4920616d20546f6d/Nintendo_Famicom_Console/CONTROLLER1/pcb_front.jpg

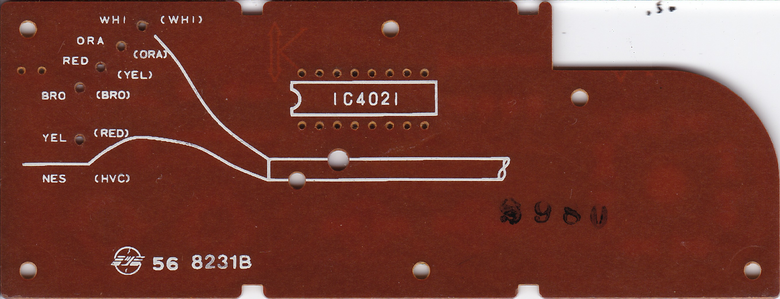
CONTROLLER1/pcb_front.jpg
