4920616d20546f6d/Nintendo_Famicom_Console/CONTROLLER2/pcb_front_fullscan.jpg

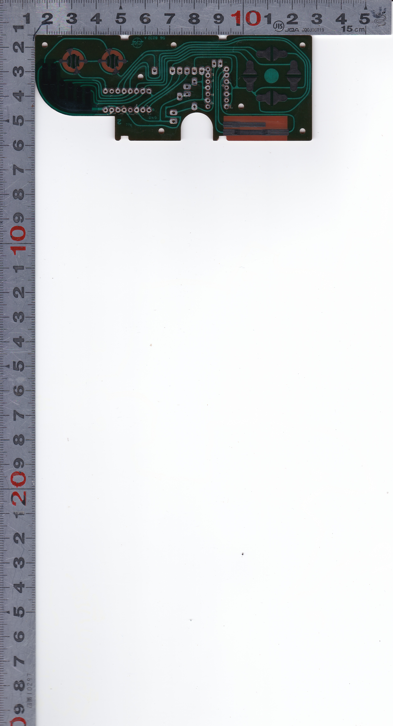
CONTROLLER2/pcb_front_fullscan.jpg
