4920616d20546f6d/Nintendo_Famicom_Console/HVC-CPU-GPM-02/pcb_rear_render.png

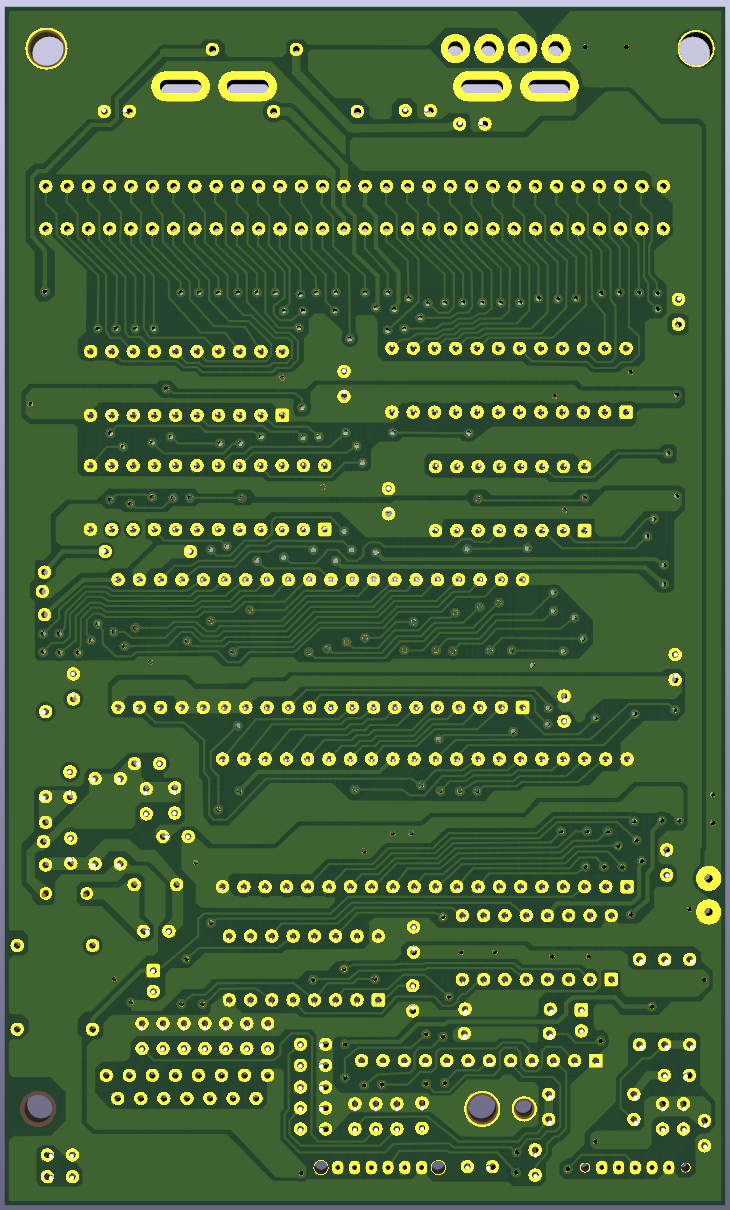
HVC-CPU-GPM-02/pcb_rear_render.png
