4920616d20546f6d/Nintendo_Famicom_Console/images/FC console RF+Power module front.jpg

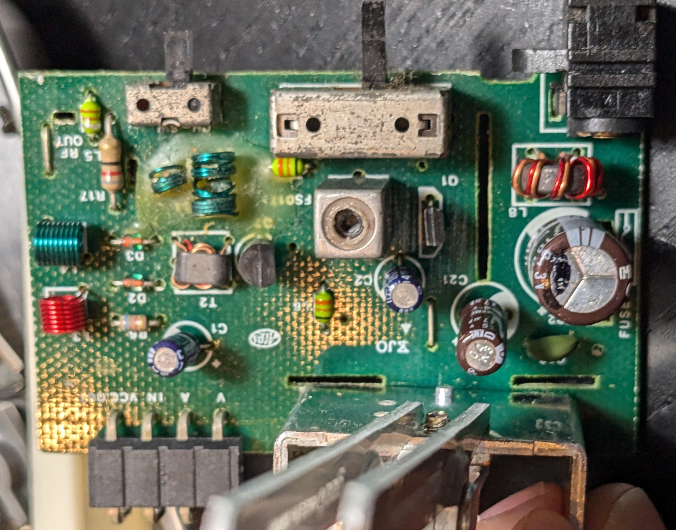
images/FC console RF+Power module front.jpg
