4920616d20546f6d/Nintendo_Famicom_Console/patents/RP2A03_-_PSG_-_Patent_Diagram_-_9.png

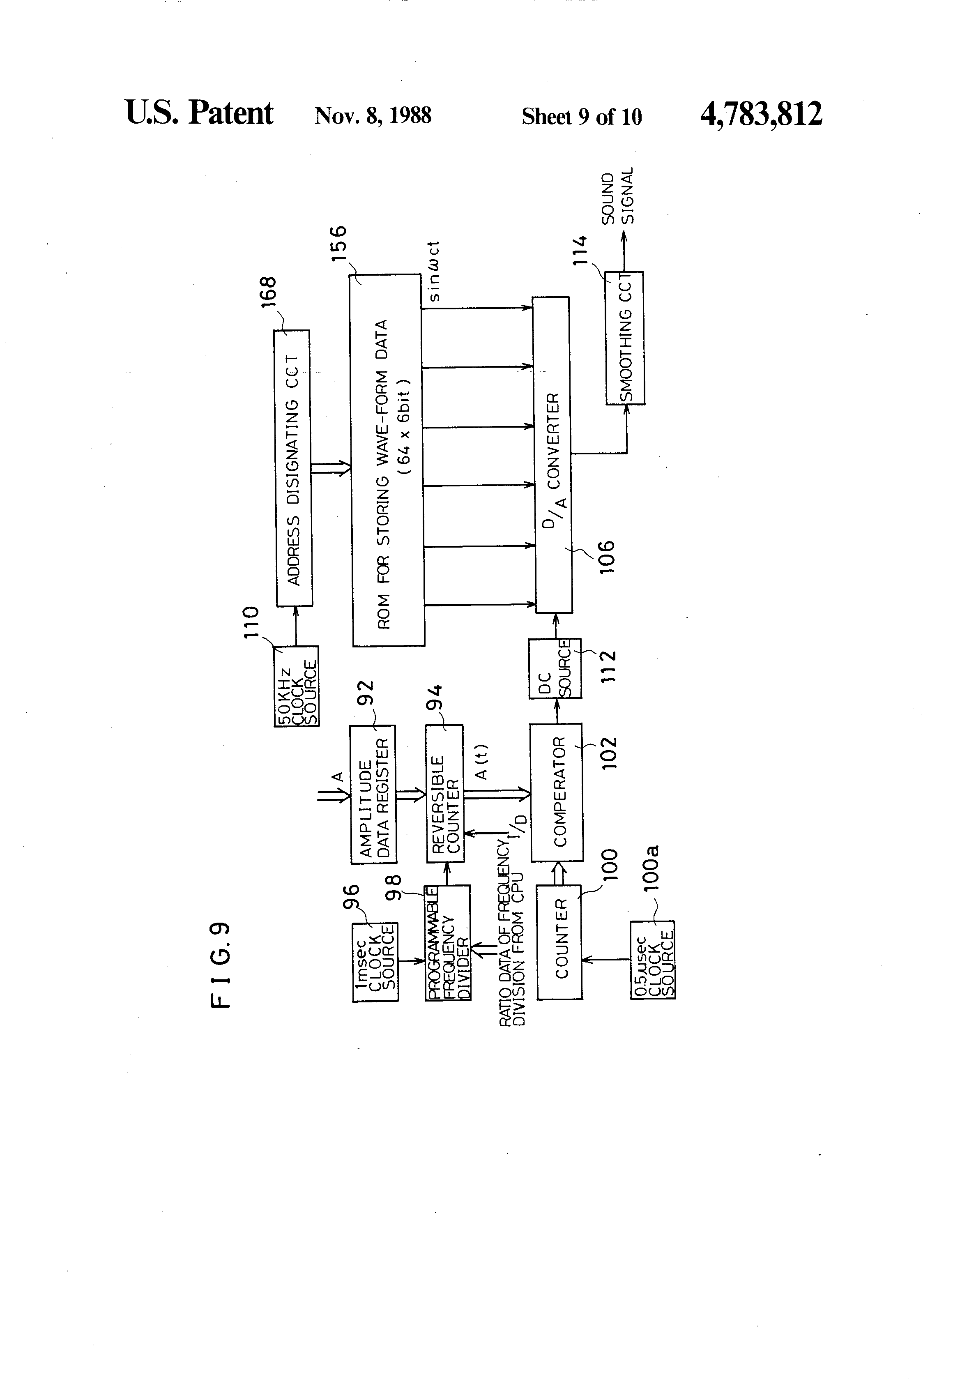
patents/RP2A03_-_PSG_-_Patent_Diagram_-_9.png
