4920616d20546f6d/Nintendo_Famicom_Console/RF_MODULE/pcb_front.jpg

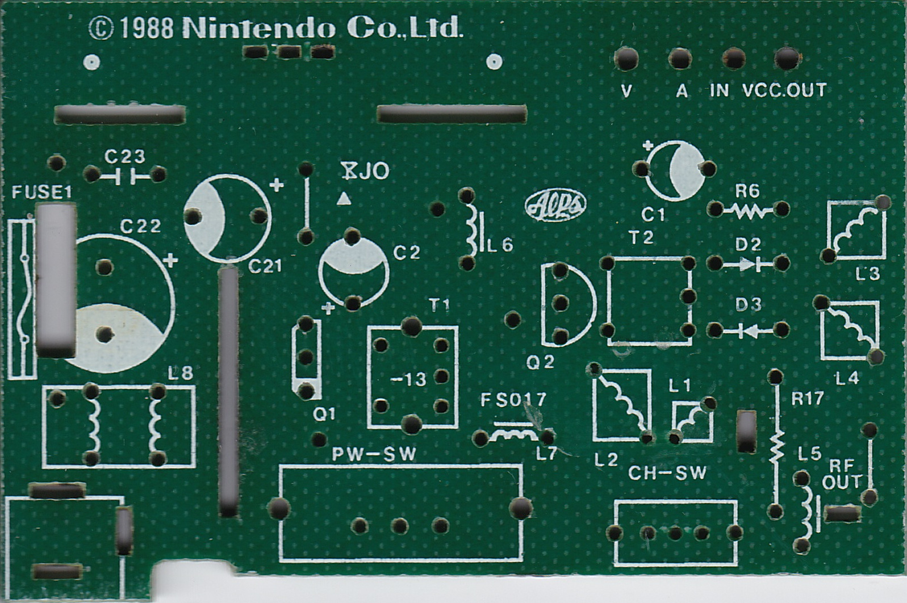
RF_MODULE/pcb_front.jpg
