4920616d20546f6d/Nintendo_Famicom_Console/RF_SWITCH/pcb_back_fullscan.jpg

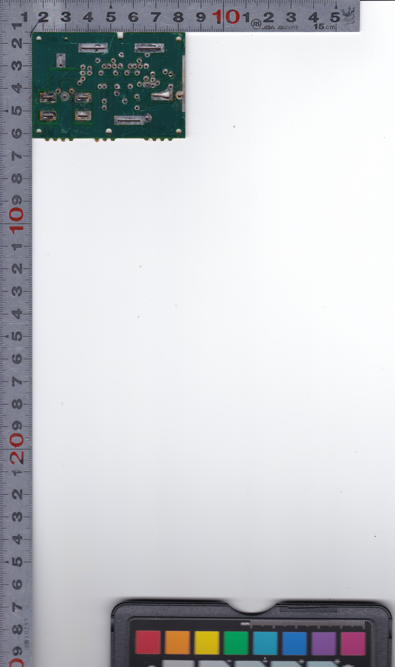
RF_SWITCH/pcb_back_fullscan.jpg
