4920616d20546f6d/Nintendo_Famicom_Console/HVC-CPU-GPM-02/HVC-CPU-GPM-02_PCB-component-side.jpg

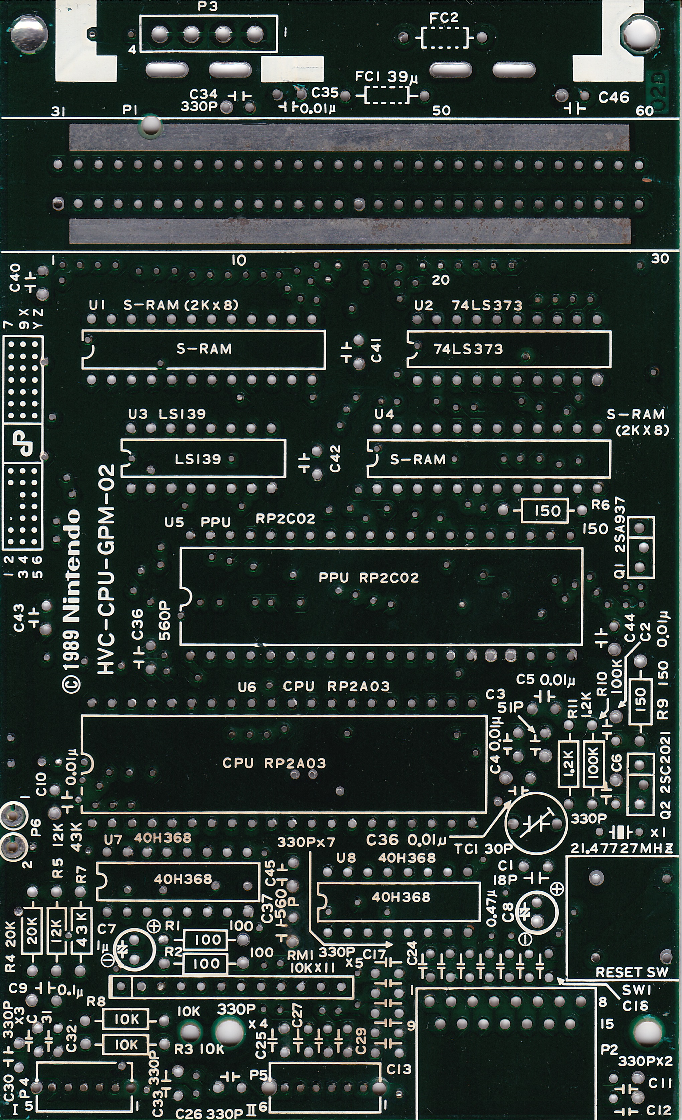
HVC-CPU-GPM-02/HVC-CPU-GPM-02_PCB-component-side.jpg
