4920616d20546f6d/Nintendo_Famicom_Console/AC_POWER/pcb_back_measure.jpg

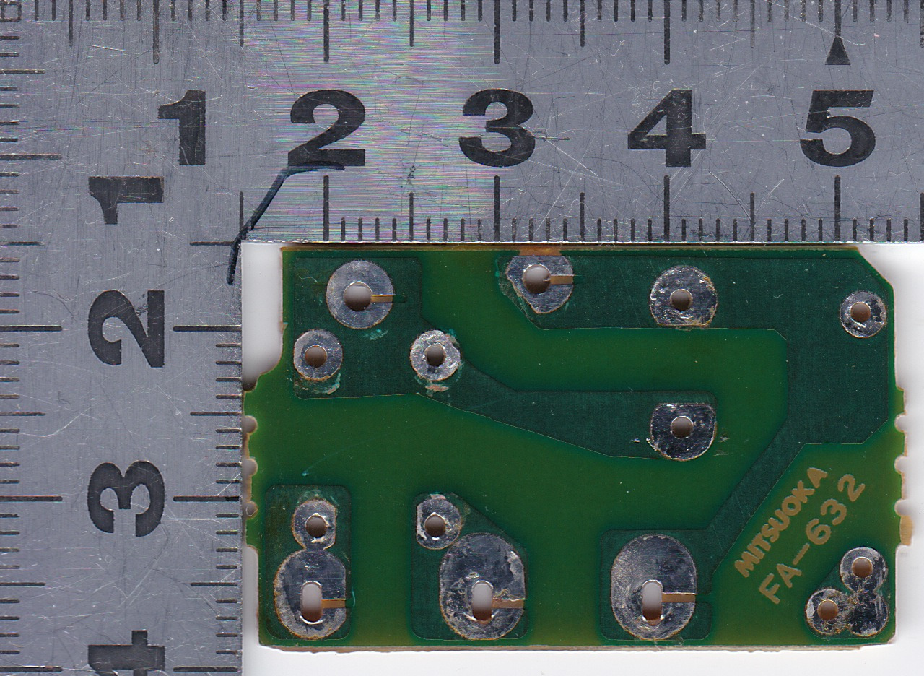
AC_POWER/pcb_back_measure.jpg
