4920616d20546f6d/Nintendo_Famicom_Console/AC_POWER/pcb_front_measure.jpg

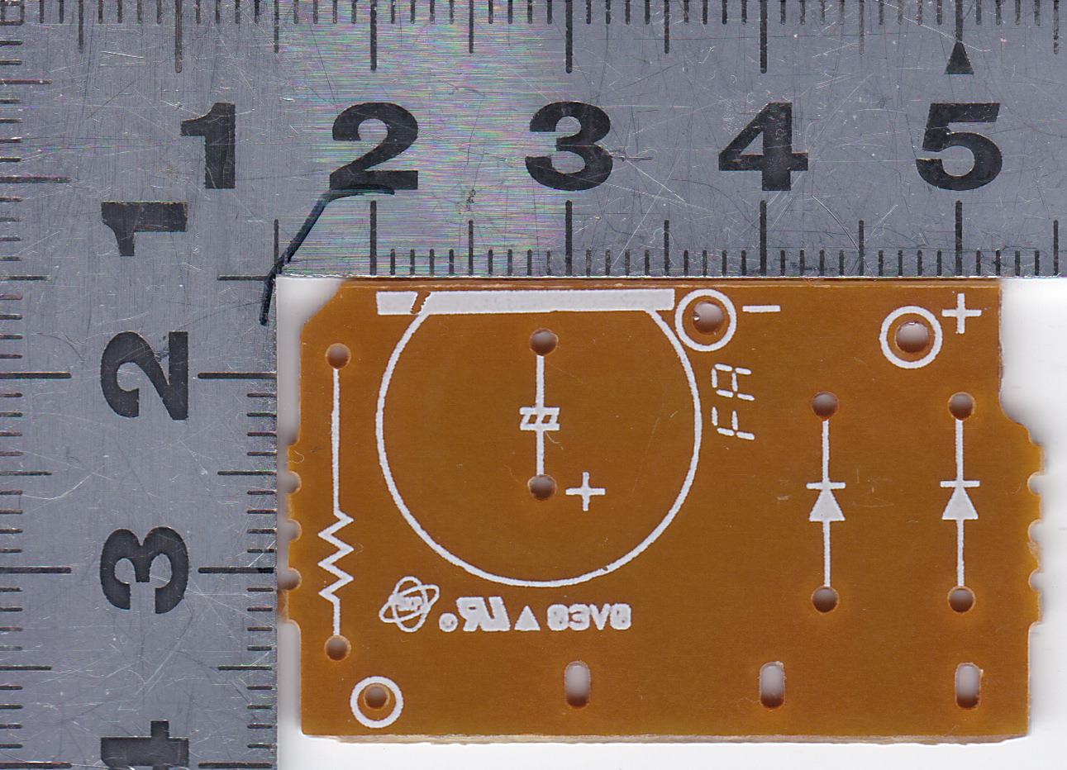
AC_POWER/pcb_front_measure.jpg
