4920616d20546f6d/Nintendo_Famicom_Console/CONTROLLER1/pcb_front_measure.jpg

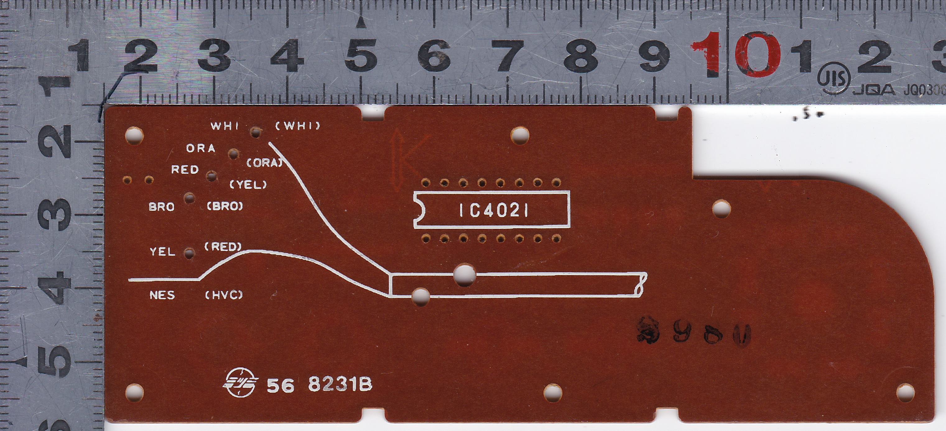
CONTROLLER1/pcb_front_measure.jpg
