4920616d20546f6d/Nintendo_Famicom_Console/HVC-CPU-07/pcb_back_measure.jpg

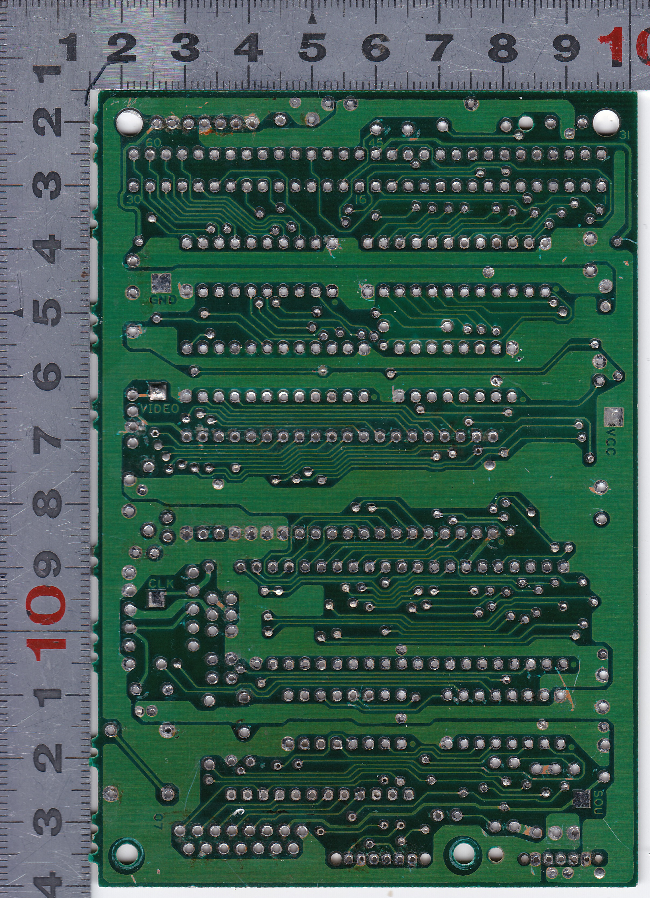
HVC-CPU-07/pcb_back_measure.jpg
