4920616d20546f6d/Nintendo_Famicom_Console/RF_MODULE/pcb_front_measure.jpg

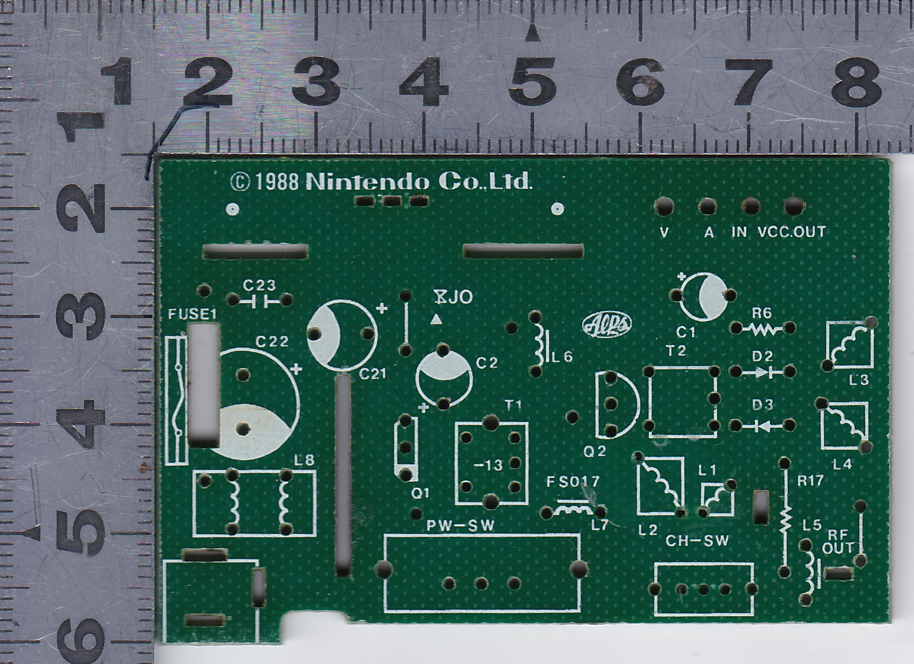
RF_MODULE/pcb_front_measure.jpg
